Spritkopf/motion-led/code/Inc/motion_sensor.h

/*
 * motion_sensor.h
 *
 *  Created on: 31.08.2017
 *      Author: ricardo
 */

#ifndef INC_MOTION_SENSOR_H_
#define INC_MOTION_SENSOR_H_

#define MOTION_SENSOR_GPIO_PIN			GPIO_PIN_1

void motion_sensor_init(void(*cb)(void));

uint8_t motion_sensor_get_state(void);

void motion_sensor_interrupt_handler();

#endif /* INC_MOTION_SENSOR_H_ */
