Spritkopf/motion-led/code/Inc/settings.h

/*
 * settings.h
 *
 *  Created on: 02.07.2016
 *      Author: Spritkopf
 *
 *      Save and restore settings in internal EEPROM memory
 *      - 10 RGB user presets, the first will be loaded on-startup
 *      - Configuration bank for device settings ... tbd
 */

#ifndef SETTINGS_H_
#define SETTINGS_H_

typedef struct
{
	uint16_t eeprom_ident;
	uint16_t angle;     /* colorwheel_angle */
	float brightness; /* brightness value */
	uint32_t adc_value;  /* light sensor value for the saved led setting */
} config_bank_t;

config_bank_t config_bank;

int8_t settings_init(void);

int8_t settings_save(void);
int8_t settings_load(void);

#endif /* SETTINGS_H_ */
